rnikitin/skadis-hex-panels/cad/two_hexes_with_jig.step

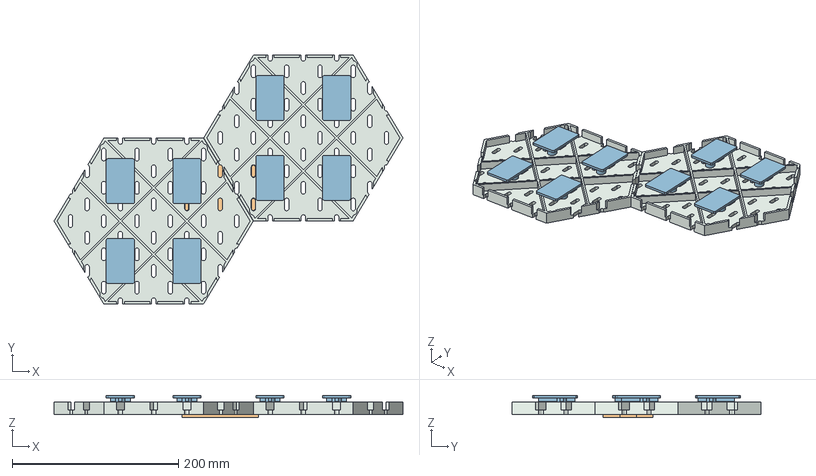
[picture p23: CAD file, 2026-10-09]
cad/two_hexes_with_jig.step
419.7 x 299.7 x 27.0 mm
panel_1
panel_1_shoe_1
panel_1_shoe_2
panel_1_shoe_3
panel_1_shoe_4
panel_2
panel_2_shoe_1
panel_2_shoe_2
panel_2_shoe_3
panel_2_shoe_4
removable_jig
