rnikitin/skadis-hex-panels/models/current/stl/corner_EXISTING_horizontal.stl

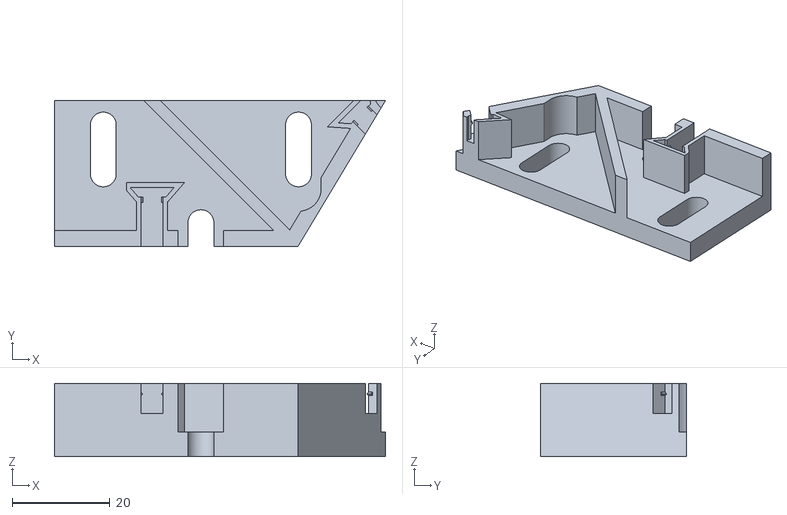
[picture p24: CAD file, 2026-10-09]
models/current/stl/corner_EXISTING_horizontal.stl
67.8 x 29.9 x 15.0
