rnikitin/skadis-hex-panels/analysis/v3/inputs/S01_long_mounted.step

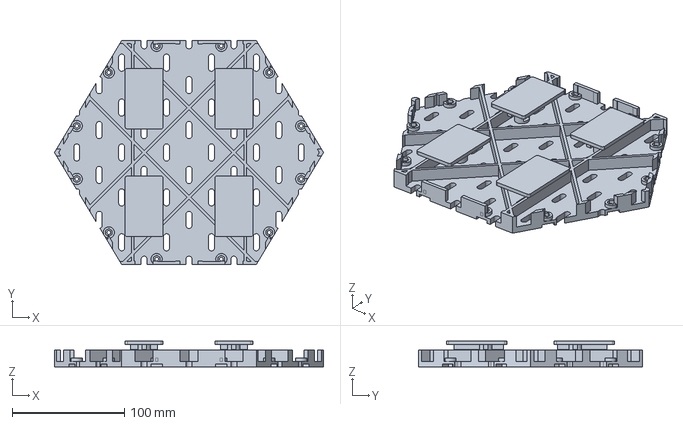
[picture p25: CAD file, 2026-10-09]
analysis/v3/inputs/S01_long_mounted.step
239.7 x 200.0 x 23.0 mm
